TweetyDaBird/Chameleon/Store images/Chameleon 4x12.png

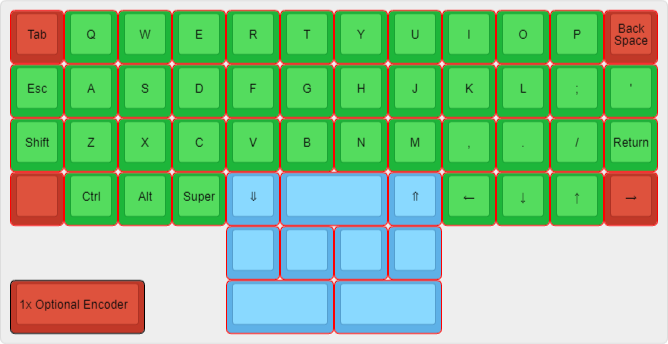
Store images/Chameleon 4x12.png
