TweetyDaBird/Chameleon/Store images/IMG_1468.JPEG

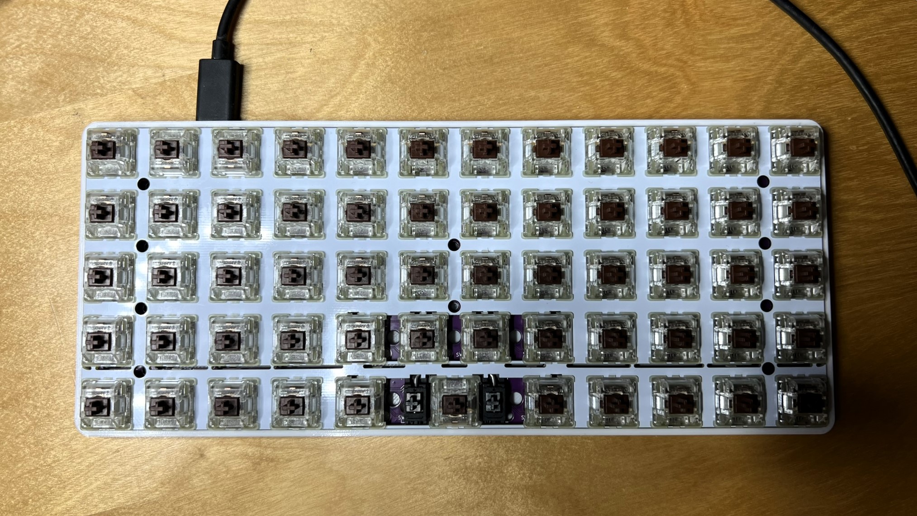
Store images/IMG_1468.JPEG
