TweetyDaBird/Chameleon/Store images/IMG_1469.JPEG

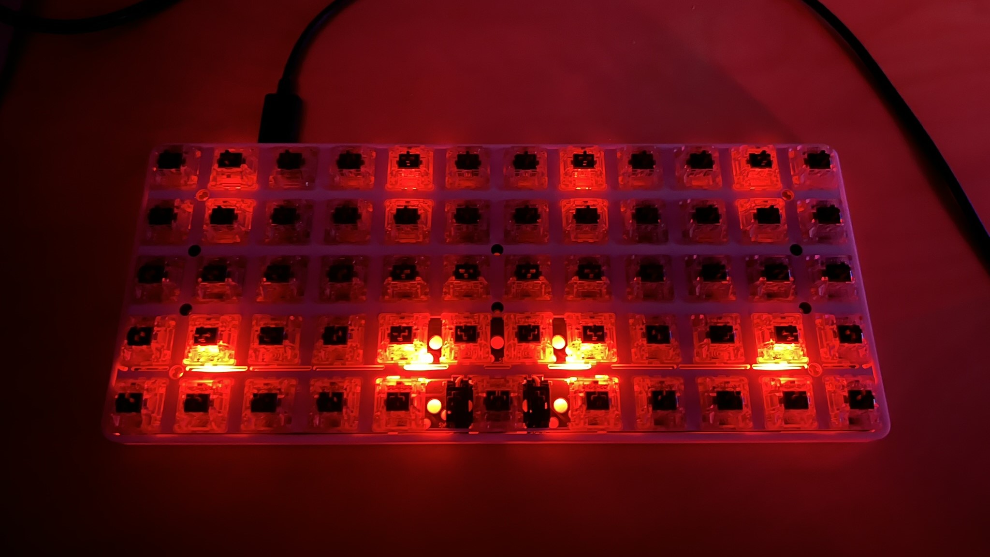
Store images/IMG_1469.JPEG
