TweetyDaBird/Chameleon/Store images/IMG_1470.JPEG

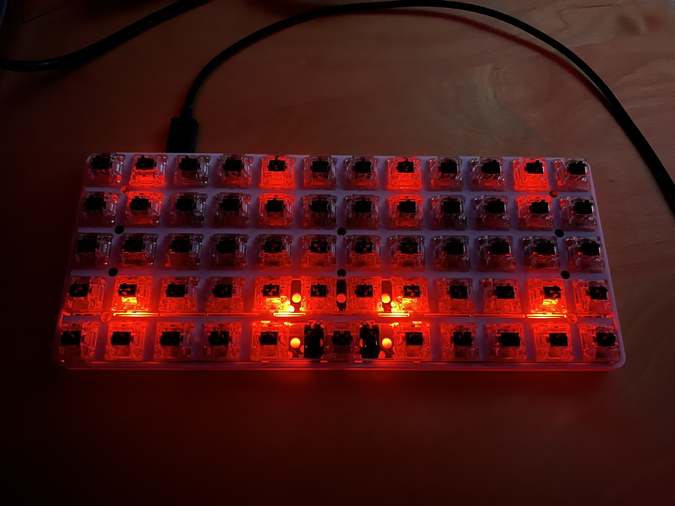
Store images/IMG_1470.JPEG
