TweetyDaBird/Chameleon/Store images/IMG_1471.JPEG

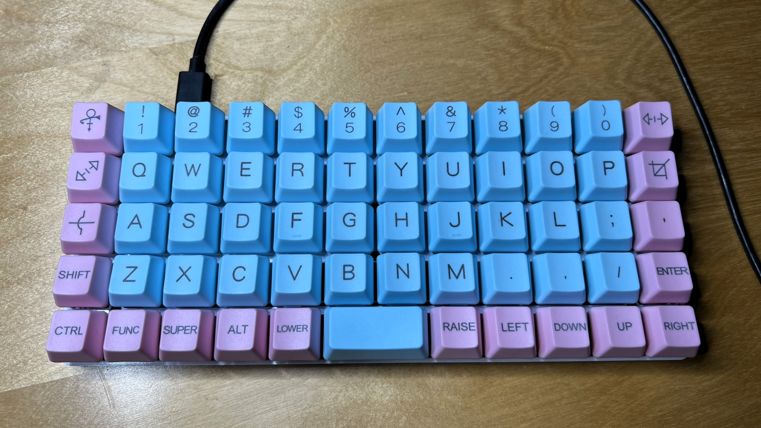
Store images/IMG_1471.JPEG
