TweetyDaBird/Chameleon/Store images/IMG_1474.JPEG

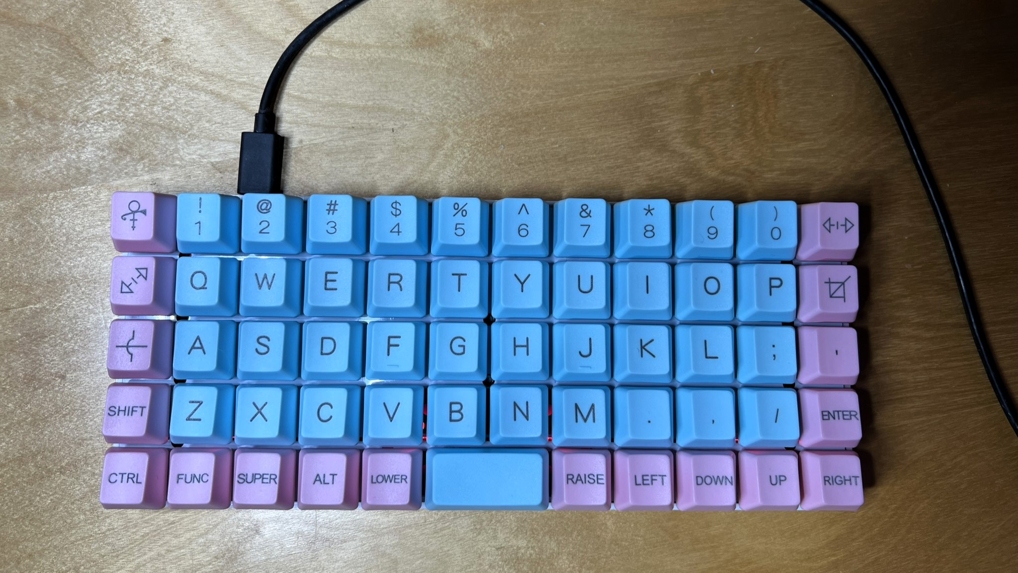
Store images/IMG_1474.JPEG
