TweetyDaBird/Chameleon/Store images/Skinny Chameleon Back.png

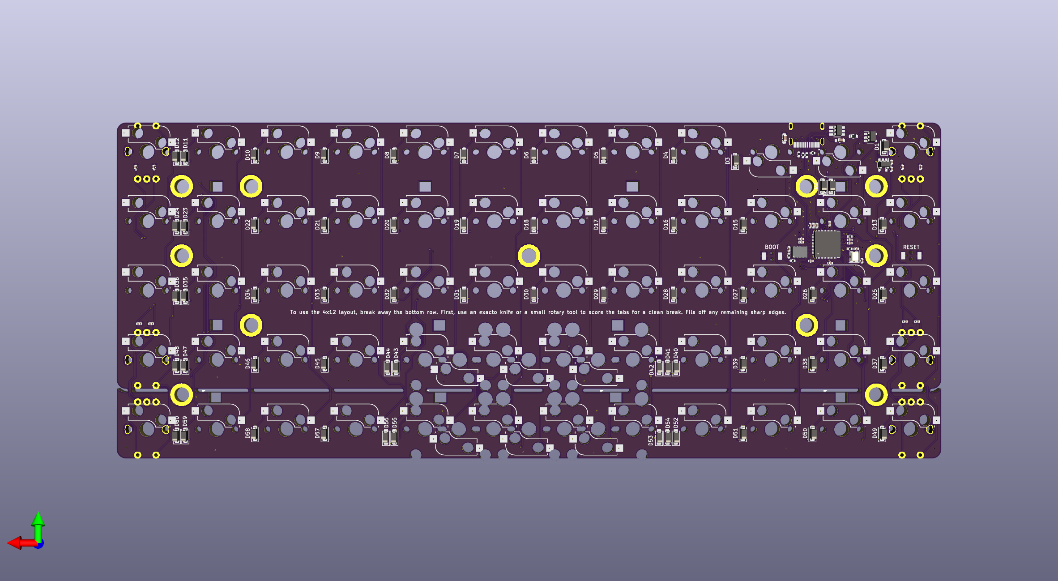
Store images/Skinny Chameleon Back.png
